jpsteckel/mintastic/Images/IMG_4772.JPEG

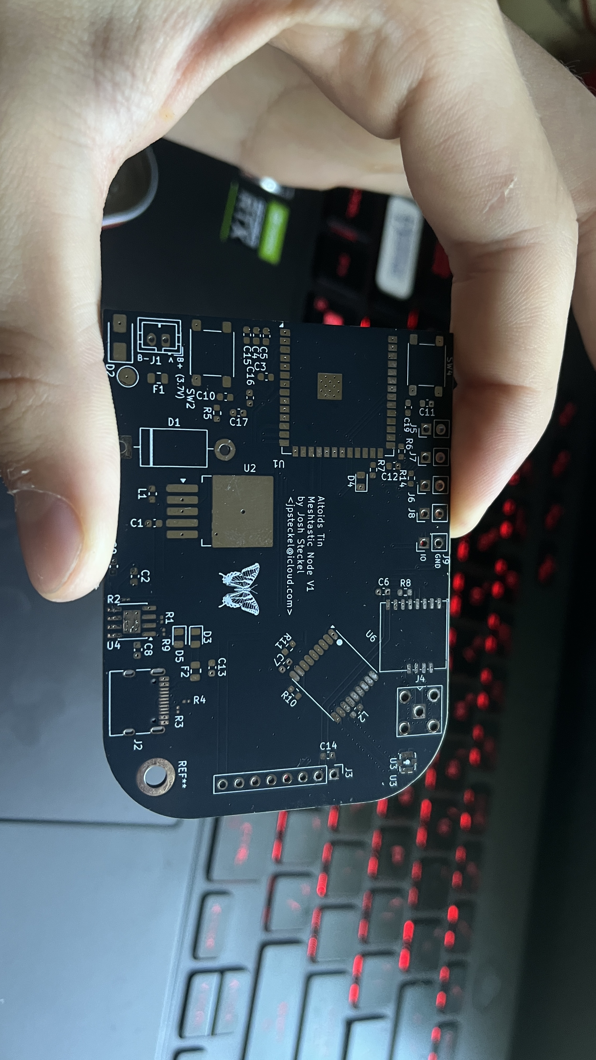
Images/IMG_4772.JPEG
